uniskie/MSXPLAYer_GameAdapter/IMAGE/title.jpg

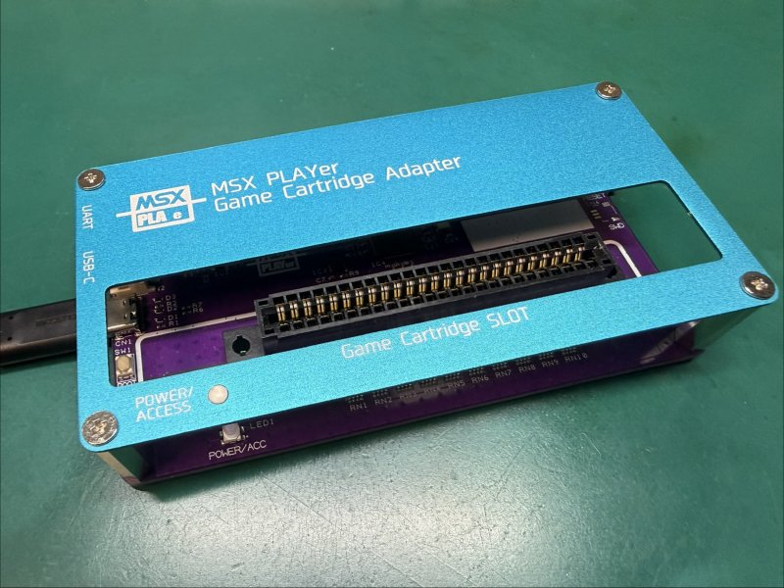
IMAGE/title.jpg
