uniskie/MSXPLAYer_GameAdapter/FIRMWARE/boards/ILF_RP2354B_MSXREADER.h

/*
 * Copyright 2026 @V9938
 * SPDX-License-Identifier: BSD-3-Clause
 */

// -----------------------------------------------------
// NOTE: THIS HEADER IS ALSO INCLUDED BY ASSEMBLER SO
//       SHOULD ONLY CONSIST OF PREPROCESSOR DIRECTIVES
// -----------------------------------------------------

#ifndef _BOARDS_ILF_RP2354B_MSXREADER_H
#define _BOARDS_ILF_RP2354B_MSXREADER_H

pico_board_cmake_set(PICO_PLATFORM, rp2350)

// For board detection
#define ILF_RP2354B_MSXREADER

// --- RP2350 VARIANT ---
// RP2354B uses the 48-GPIO B package with integrated flash.
#define PICO_RP2350A 0

// --- UART ---
#ifndef PICO_DEFAULT_UART
#define PICO_DEFAULT_UART 0
#endif
#ifndef PICO_DEFAULT_UART_TX_PIN
#define PICO_DEFAULT_UART_TX_PIN 0
#endif
#ifndef PICO_DEFAULT_UART_RX_PIN
#define PICO_DEFAULT_UART_RX_PIN 1
#endif

// --- WS2812 ---
#ifndef PICO_DEFAULT_WS2812_PIN
#define PICO_DEFAULT_WS2812_PIN 4
#endif

// --- FLASH ---
#define PICO_BOOT_STAGE2_CHOOSE_W25Q080 1

#ifndef PICO_FLASH_SPI_CLKDIV
#define PICO_FLASH_SPI_CLKDIV 2
#endif

pico_board_cmake_set_default(PICO_FLASH_SIZE_BYTES, (2 * 1024 * 1024))
#ifndef PICO_FLASH_SIZE_BYTES
#define PICO_FLASH_SIZE_BYTES (2 * 1024 * 1024)
#endif

pico_board_cmake_set_default(PICO_RP2350_A2_SUPPORTED, 1)
#ifndef PICO_RP2350_A2_SUPPORTED
#define PICO_RP2350_A2_SUPPORTED 1
#endif

#endif
